swidzi/G1000---PCB-designs/Rotary Encoder Breakout/Rotary Encoder Breakout.brd

## EAGLE design Rotary Encoder Breakout/Rotary Encoder Breakout.brd (2021-01-18)

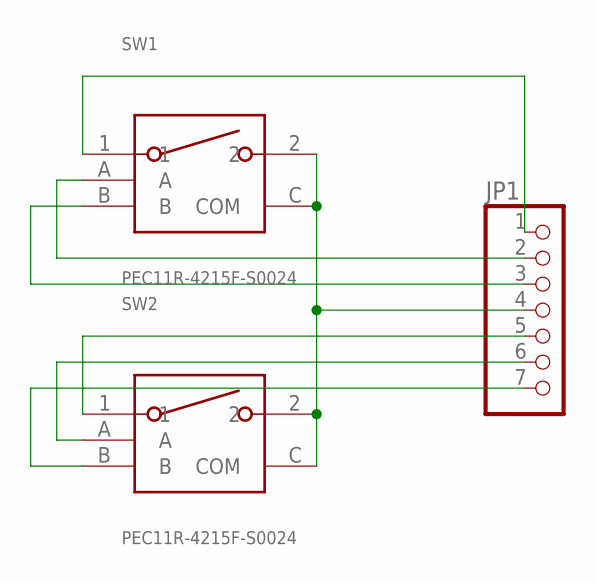
[picture p23: schematic Rotary Encoder Breakout.sch]

Parts:
JP1: PINHD-1X07_2.54-90°; 1X07/90
SW1, SW2: PEC11R-4215F-S0024

Connections:
unnamed: JP1.4, SW1.2, SW1.C (COM), SW2.2, SW2.C (COM)
unnamed: JP1.5, SW2.1
unnamed: JP1.6, SW2.A
unnamed: JP1.7, SW2.B
unnamed: JP1.1, SW1.1
unnamed: JP1.2, SW1.A
unnamed: JP1.3, SW1.B

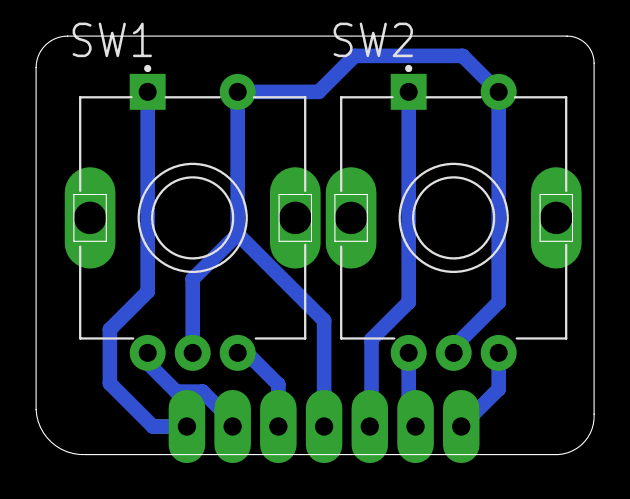
[picture p24: board Rotary Encoder Breakout/Rotary Encoder Breakout.brd from above]

Board: 2 copper layers, 31.0 x 23.2 mm, 3 parts (1 on the bottom side), 7 nets.
