swidzi/G1000---PCB-designs/Rotary Encoder Breakout 2/Rotary Encoder Breakout.brd

## EAGLE design Rotary Encoder Breakout 2/Rotary Encoder Breakout.brd (2021-01-18)

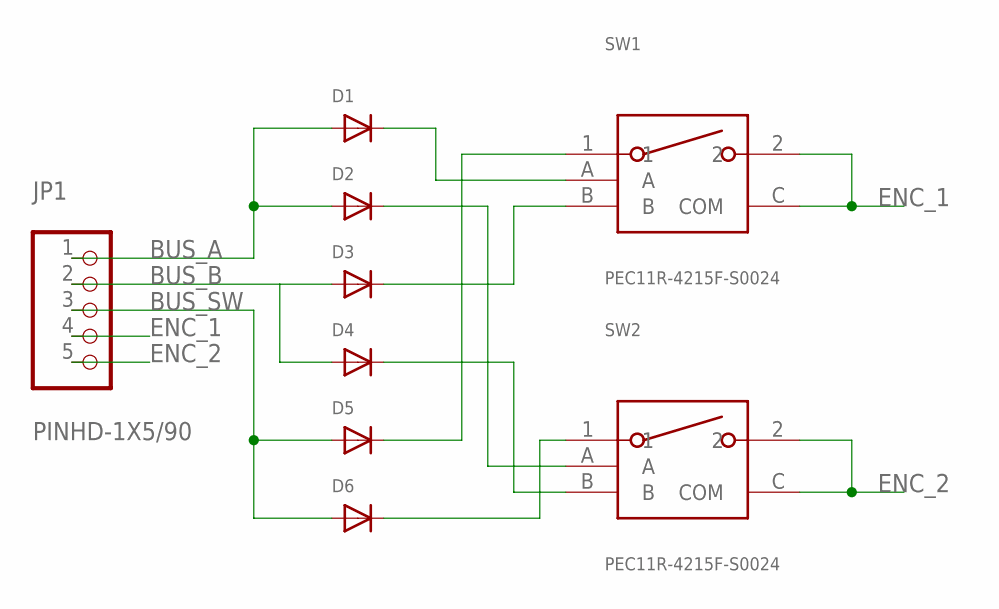
[picture p25: schematic Rotary Encoder Breakout.sch]

Parts:
D1, D2, D3, D4, D5, D6: DIODESOD-123; SOD-123
JP1: PINHD-1X5/90; 1X05/90
SW1, SW2: PEC11R-4215F-S0024

Connections:
BUS_A: D1.A, D2.A, JP1.1
BUS_B: D3.A, D4.A, JP1.2
BUS_SW: D5.A, D6.A, JP1.3
ENC_1: JP1.4, SW1.2, SW1.C (COM)
ENC_2: JP1.5, SW2.2, SW2.C (COM)
unnamed: D1.C, SW1.A
unnamed: D2.C, SW2.A
unnamed: D3.C, SW1.B
unnamed: D4.C, SW2.B
unnamed: D5.C, SW1.1
unnamed: D6.C, SW2.1

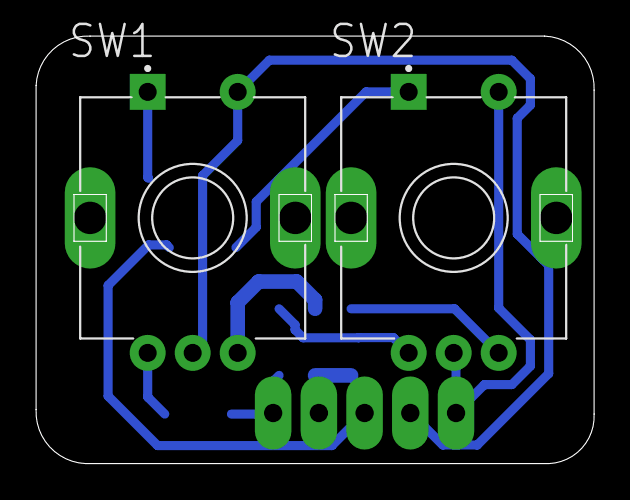
[picture p26: board Rotary Encoder Breakout 2/Rotary Encoder Breakout.brd from above]

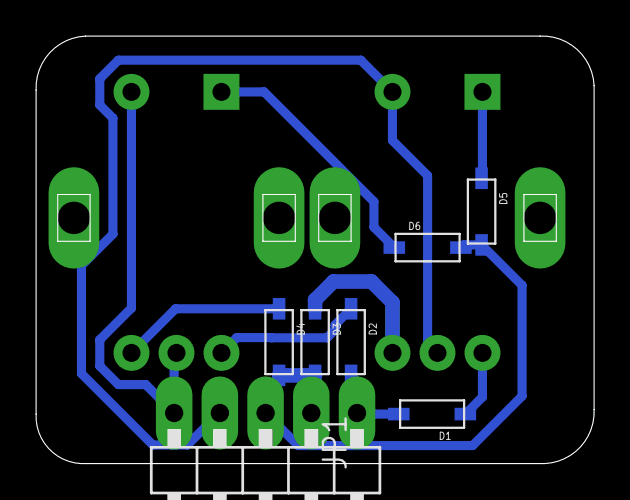
[picture p27: board Rotary Encoder Breakout 2/Rotary Encoder Breakout.brd from below]

Board: 2 copper layers, 31.0 x 23.8 mm, 9 parts (7 on the bottom side), 11 nets.
